alvarogal/sensor_de_temperatura_embebido/buildroot-2013.08.1/board/boundarydevices/nitrogen6x/readme.txt

Buildroot for Boundary Devices Nitrogen6X:

http://boundarydevices.com/products/nitrogen6x-board-imx6-arm-cortex-a9-sbc/

To install, simply extract rootfs.ext2 to first partition of a uSD card:

sudo dd if=output/images/rootfs.ext2 of=/dev/sdX1

Where 'sdX1' is the device node of the uSD partition.
