alvarogal/sensor_de_temperatura_embebido/SPI_test/testKernelOrg/prueba_T_a_vcc.png

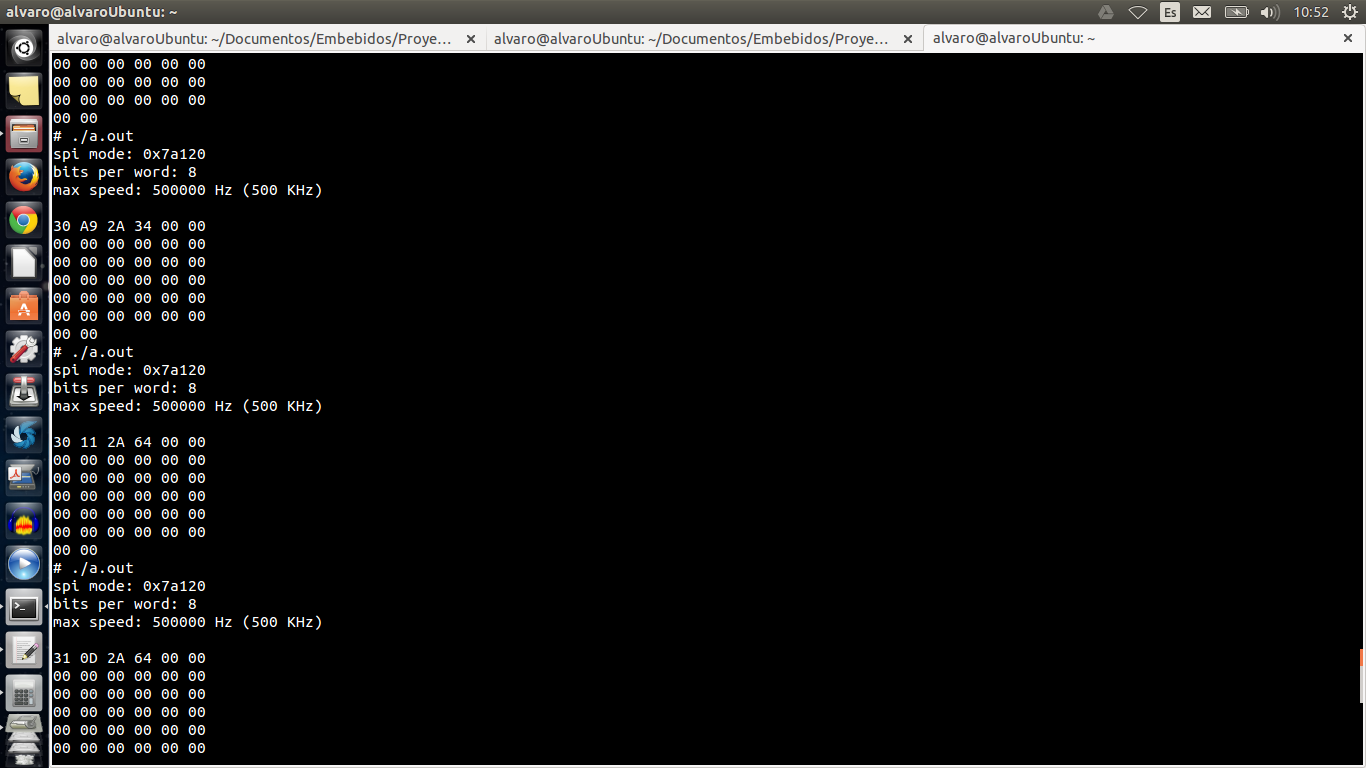
SPI_test/testKernelOrg/prueba_T_a_vcc.png
