alvarogal/sensor_de_temperatura_embebido/hija3/hija3.sch

## KiCad design hija3/hija3.sch (2014-12-09)

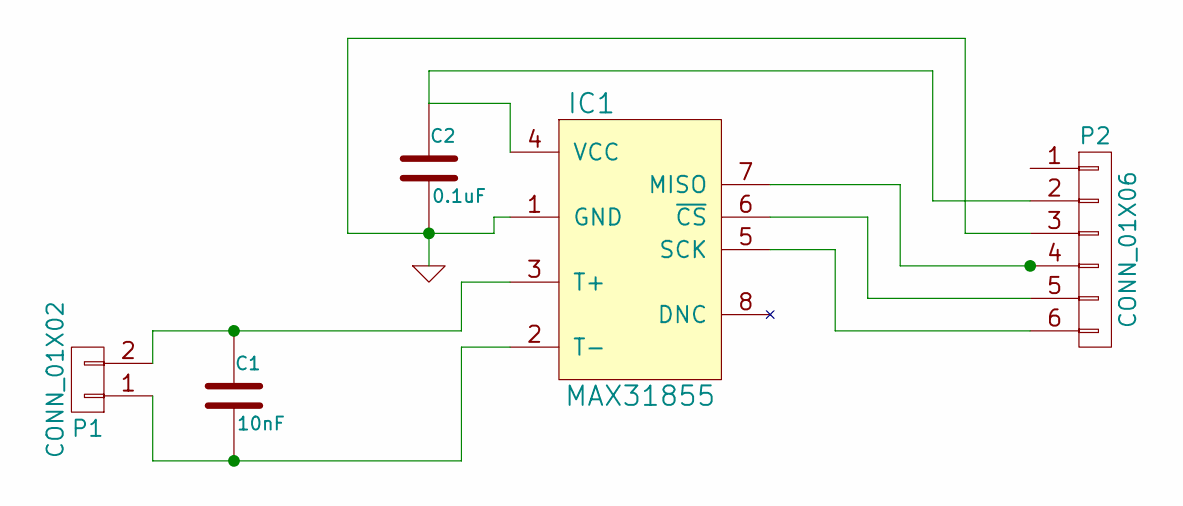
[picture p23: schematic hija3.sch]

Parts:
C1: 10nF; SMD-0805
C2: 0.1uF; SMD-0805
IC1: MAX31855; SOIC-8-N; Part MAX31855[K,J,N,S,T,E,R]ASA+
P1: CONN_01X02; bornier2
P2: CONN_01X06; Pin_Header_Straight_1x06

Connections:
GND: C2.2, IC1.1 (GND), P2.3
unnamed: C1.1, IC1.3 (T+), P1.2
unnamed: C1.2, IC1.2 (T-), P1.1
unnamed: C2.1, IC1.4 (VCC), P2.2
unnamed: IC1.5 (SCK), P2.6
unnamed: IC1.6 (~CS~), P2.5
unnamed: IC1.7 (MISO), P2.4
