alvarogal/sensor_de_temperatura_embebido/SPI_test/no_funcionan/olimexMODTC/MOD-TC/OLIMEX.h

/******************************************************************************/
/* OLIMEX COMMANDS	                                                      */
/******************************************************************************/
#ifndef _OLIMEX_H
#define _OLIMEX_H

#define	SET_TRIS	0x01
#define SET_LAT		0x02
#define	GET_PORT	0x03
#define SET_PU		0x04

#define GET_AN0		0x10
#define GET_AN1		0x11
#define GET_AN2		0x12
#define GET_AN6		0x16
#define GET_AN7		0x17

#define GET_TEMP	0x21
#define SET_ADDRESS	0xF0
#define GET_ID		0x20
#define DEVICE_ID	0x27

#endif
